FreyaAmiga/tf530/docs/IMG_5832.JPG

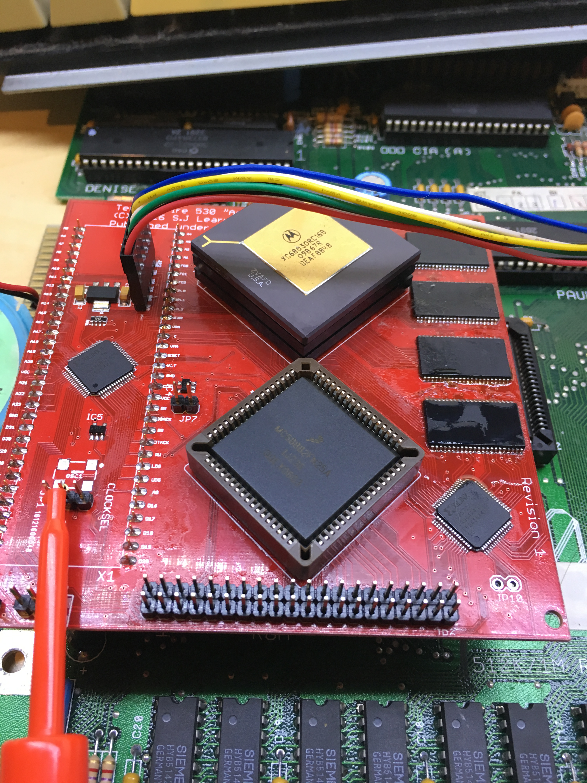
docs/IMG_5832.JPG
