FreyaAmiga/tf530/docs/IMG_5966.JPG

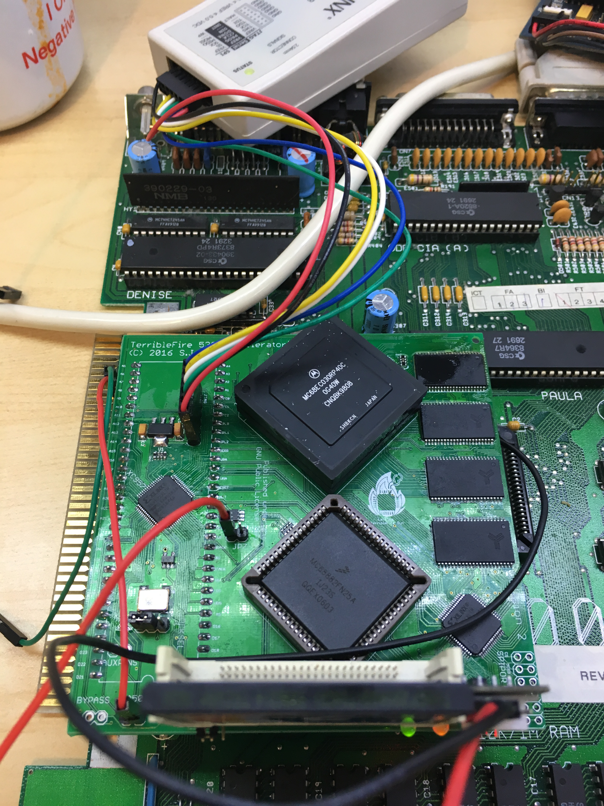
docs/IMG_5966.JPG
